KN-Hardwire/Electronic-Flute/software/include/notes.h

#ifndef NOTES_H
#define NOTES_H

// Note Frequencies [Hz]
#define NOTE_C4		((float) 261.63)
#define NOTE_CS4	((float) 277.18)
#define NOTE_D4		((float) 293.66)
#define NOTE_DS4	((float) 311.13)
#define NOTE_E4		((float) 329.63)
#define NOTE_F4		((float) 349.23)
#define NOTE_FS4	((float) 369.99)
#define NOTE_G4		((float) 392.00)
#define NOTE_GS4	((float) 415.30)
#define NOTE_A4		((float) 440.00)
#define NOTE_AS4	((float) 466.16)
#define NOTE_B4		((float) 493.88)
#define NOTE_C5		((float) 523.25)
#define NOTE_D5		((float) 587.33)
#define NOTE_CS5	((float) 554.37)
#define NOTE_DS5	((float) 622.25)
#define NOTE_E5		((float) 659.25)
#define NOTE_F5		((float) 698.46)
#define NOTE_G5		((float) 783.99)
#define NOTE_GS5	((float) 830.61)
#define NOTE_A5		((float) 880.00)
#define NOTE_AS5	((float) 932.33)
#define NOTE_B5		((float) 987.77)

extern float mask_freq[256];
#endif
