KN-Hardwire/Electronic-Flute/software/source/notes.c

#include "notes.h"

float mask_freq[256] = {
	NOTE_C4, NOTE_C4, NOTE_C4, NOTE_C4, NOTE_C4, NOTE_C4, NOTE_C4, NOTE_C4,
	NOTE_C4, NOTE_C4, NOTE_C4, NOTE_C4, NOTE_C4, NOTE_C4, NOTE_C4, NOTE_C4,
	NOTE_C4, NOTE_C4, NOTE_C4, NOTE_C4, NOTE_C4, NOTE_C4, NOTE_C4, NOTE_C4,
	NOTE_C4, NOTE_C4, NOTE_C4, NOTE_C4, NOTE_C4, NOTE_C4, NOTE_C4, NOTE_C4,
	NOTE_CS4, NOTE_C4, NOTE_C4, NOTE_C4, NOTE_C4, NOTE_C4, NOTE_C4, NOTE_C4,
	NOTE_C4, NOTE_C4, NOTE_C4, NOTE_C4, NOTE_C4, NOTE_C4, NOTE_C4, NOTE_C4,
	NOTE_C4, NOTE_C4, NOTE_C4, NOTE_C4, NOTE_C4, NOTE_C4, NOTE_C4, NOTE_C4,
	NOTE_C4, NOTE_C4, NOTE_C4, NOTE_C4, NOTE_C4, NOTE_C4, NOTE_C4, NOTE_C4,
	NOTE_D4, NOTE_D4, NOTE_D4, NOTE_D4, NOTE_D4, NOTE_D4, NOTE_D4, NOTE_D4,
	NOTE_D4, NOTE_D4, NOTE_D4, NOTE_D4, NOTE_D4, NOTE_D4, NOTE_D4, NOTE_D4,
	NOTE_DS4, NOTE_D4, NOTE_D4, NOTE_D4, NOTE_D4, NOTE_D4, NOTE_D4, NOTE_D4,
	NOTE_D4, NOTE_D4, NOTE_D4, NOTE_D4, NOTE_D4, NOTE_D4, NOTE_D4, NOTE_D4,
	NOTE_E4, NOTE_E4, NOTE_E4, NOTE_E4, NOTE_GS4, NOTE_E4, NOTE_E4, NOTE_E4,
	NOTE_FS4, NOTE_E4, NOTE_E4, NOTE_E4, NOTE_E4, NOTE_E4, NOTE_E4, NOTE_E4,
	NOTE_F4, NOTE_F4, NOTE_F4, NOTE_F4, NOTE_F4, NOTE_F4, NOTE_F4, NOTE_F4,
	NOTE_G4, NOTE_G4, NOTE_AS4, NOTE_G4, NOTE_A4, NOTE_C5, NOTE_B4, NOTE_CS5,
	NOTE_C5, NOTE_B5, NOTE_C5, NOTE_C5, NOTE_C5, NOTE_C5, NOTE_C5, NOTE_C5,
	NOTE_C5, NOTE_C5, NOTE_C5, NOTE_C5, NOTE_C5, NOTE_C5, NOTE_C5, NOTE_C5,
	NOTE_C5, NOTE_C5, NOTE_C5, NOTE_C5, NOTE_C5, NOTE_C5, NOTE_C5, NOTE_C5,
	NOTE_C5, NOTE_C5, NOTE_C5, NOTE_C5, NOTE_C5, NOTE_C5, NOTE_C5, NOTE_C5,
	NOTE_C5, NOTE_C5, NOTE_C5, NOTE_C5, NOTE_C5, NOTE_C5, NOTE_C5, NOTE_C5,
	NOTE_C5, NOTE_C5, NOTE_C5, NOTE_C5, NOTE_C5, NOTE_C5, NOTE_C5, NOTE_C5,
	NOTE_C5, NOTE_C5, NOTE_C5, NOTE_C5, NOTE_C5, NOTE_C5, NOTE_C5, NOTE_C5,
	NOTE_C5, NOTE_C5, NOTE_C5, NOTE_C5, NOTE_C5, NOTE_C5, NOTE_C5, NOTE_C5,
	NOTE_DS5, NOTE_DS5, NOTE_DS5, NOTE_DS5, NOTE_DS5, NOTE_DS5, NOTE_DS5, NOTE_DS5,
	NOTE_DS5, NOTE_DS5, NOTE_DS5, NOTE_DS5, NOTE_DS5, NOTE_DS5, NOTE_DS5, NOTE_DS5,
	NOTE_DS5, NOTE_DS5, NOTE_DS5, NOTE_DS5, NOTE_DS5, NOTE_DS5, NOTE_DS5, NOTE_DS5,
	NOTE_DS5, NOTE_DS5, NOTE_DS5, NOTE_DS5, NOTE_DS5, NOTE_DS5, NOTE_DS5, NOTE_DS5,
	NOTE_E5, NOTE_E5, NOTE_E5, NOTE_E5, NOTE_E5, NOTE_E5, NOTE_E5, NOTE_E5,
	NOTE_E5, NOTE_E5, NOTE_E5, NOTE_E5, NOTE_E5, NOTE_E5, NOTE_E5, NOTE_E5,
	NOTE_F5, NOTE_F5, NOTE_F5, NOTE_F5, NOTE_F5, NOTE_F5, NOTE_F5, NOTE_F5,
	NOTE_G5, NOTE_G5, NOTE_G5, NOTE_G5, NOTE_G5, NOTE_D5, NOTE_D5, NOTE_C5
};
